rafaelmartins/fightstick/sch/fightstick.kicad_sch

## KiCad design sch/fightstick.kicad_sch (2026-01-09)

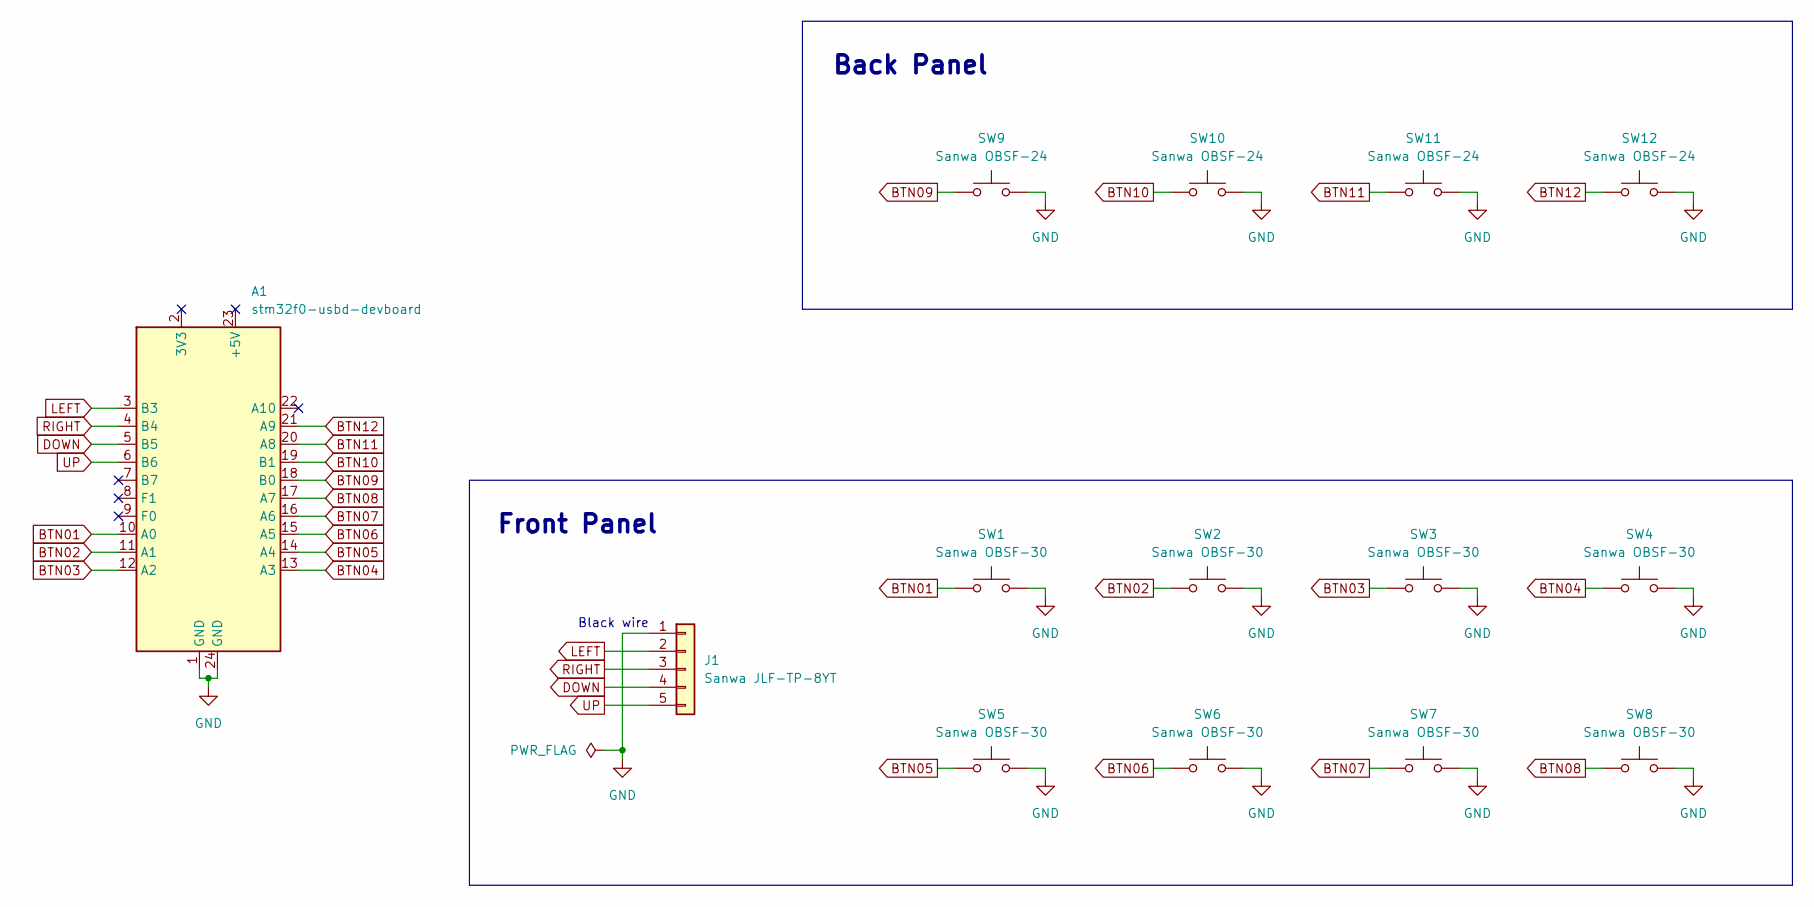
[picture p6: schematic fightstick.kicad_sch]

Parts:
A1: stm32f0-usbd-devboard
J1: Sanwa JLF-TP-8YT
SW1, SW2, SW3, SW4, SW5, SW6, SW7, SW8: Sanwa OBSF-30
SW9, SW10, SW11, SW12: Sanwa OBSF-24

Connections:
BTN01: A1.10 (A0), SW1.1
BTN02: A1.11 (A1), SW2.1
BTN03: A1.12 (A2), SW3.1
BTN04: A1.13 (A3), SW4.1
BTN05: A1.14 (A4), SW5.1
BTN06: A1.15 (A5), SW6.1
BTN07: A1.16 (A6), SW7.1
BTN08: A1.17 (A7), SW8.1
BTN09: A1.18 (B0), SW9.1
BTN10: A1.19 (B1), SW10.1
BTN11: A1.20 (A8), SW11.1
BTN12: A1.21 (A9), SW12.1
DOWN: A1.5 (B5), J1.4
GND: A1.1 (GND), A1.24 (GND), J1.1, SW1.2, SW2.2, SW3.2, SW4.2, SW5.2, SW6.2, SW7.2, SW8.2, SW9.2, SW10.2, SW11.2, SW12.2
LEFT: A1.3 (B3), J1.2
RIGHT: A1.4 (B4), J1.3
UP: A1.6 (B6), J1.5

Notes on the sheet:
Front Panel
Black wire
Back Panel
