rafaelmartins/fightstick/firmware/descriptors.c

// SPDX-FileCopyrightText: 2026 Rafael G. Martins <rafael@rafaelmartins.eng.br>
// SPDX-License-Identifier: BSD-3-Clause

#include <stdlib.h>

#include <usbd.h>
#include <usb-std-hid.h>

#define MANUFACTURER u"rgm.io"
#define PRODUCT      u"fightstick"

#define ID_VENDOR  0x1d50
#define ID_PRODUCT 0x619a

// +----------+-------+-------------------+
// | ReportId | Kind  | ReportSizeInBytes |
// +----------+-------+-------------------+
// |        1 | Input |                 2 |
// +----------+-------+-------------------+
static const uint8_t hid_report_descriptor[] =
{
    0x05, 0x01,    // UsagePage(Generic Desktop[0x0001])
    0x09, 0x05,    // UsageId(Gamepad[0x0005])
    0xA1, 0x01,    // Collection(Application)
    0x85, 0x01,    //     ReportId(1)
    0x09, 0x01,    //     UsageId(Pointer[0x0001])
    0xA1, 0x00,    //     Collection(Physical)
    0x09, 0x30,    //         UsageId(X[0x0030])
    0x09, 0x31,    //         UsageId(Y[0x0031])
    0x15, 0xFF,    //         LogicalMinimum(-1)
    0x25, 0x01,    //         LogicalMaximum(1)
    0x95, 0x02,    //         ReportCount(2)
    0x75, 0x02,    //         ReportSize(2)
    0x81, 0x02,    //         Input(Data, Variable, Absolute, NoWrap, Linear, PreferredState, NoNullPosition, BitField)
    0xC0,          //     EndCollection()
    0x05, 0x09,    //     UsagePage(Button[0x0009])
    0x19, 0x01,    //     UsageIdMin(Button 1[0x0001])
    0x29, 0x0C,    //     UsageIdMax(Button 12[0x000C])
    0x15, 0x00,    //     LogicalMinimum(0)
    0x95, 0x0C,    //     ReportCount(12)
    0x75, 0x01,    //     ReportSize(1)
    0x81, 0x02,    //     Input(Data, Variable, Absolute, NoWrap, Linear, PreferredState, NoNullPosition, BitField)
    0xC0,          // EndCollection()
};

static const usb_device_descriptor_t device_descriptor = {
    .bLength = sizeof(usb_device_descriptor_t),
    .bDescriptorType = USB_DESCR_TYPE_DEVICE,
    .bcdUSB = 0x0200,
    .bDeviceClass = 0,
    .bDeviceSubClass = 0,
    .bDeviceProtocol = 0,
    .bMaxPacketSize0 = USBD_EP0_SIZE,
    .idVendor = ID_VENDOR,
    .idProduct = ID_PRODUCT,
    .bcdDevice = 0x0101,
    .iManufacturer = 1,
    .iProduct = 2,
    .iSerialNumber = 3,
    .bNumConfigurations = 1,
};

const usb_device_descriptor_t*
usbd_get_device_descriptor_cb(void)
{
    return &device_descriptor;
}


typedef struct __attribute__((packed)) {
    usb_config_descriptor_t config_descriptor;
    usb_interface_descriptor_t interface_descriptor;
    usb_hid_descriptor_t hid_descriptor;
    usb_endpoint_descriptor_t endpoint_in_descriptor;
} config_descriptor_t;

static const config_descriptor_t config_descriptor = {
    .config_descriptor = {
        .bLength = sizeof(usb_config_descriptor_t),
        .bDescriptorType = USB_DESCR_TYPE_CONFIGURATION,
        .wTotalLength = sizeof(config_descriptor_t),
        .bNumInterfaces = 1,
        .bConfigurationValue = 1,
        .iConfiguration = 0,
        .bmAttributes = USB_DESCR_CONFIG_ATTR_RESERVED,
        .bMaxPower = 20, // 40mA
    },
    .interface_descriptor = {
        .bLength = sizeof(usb_interface_descriptor_t),
        .bDescriptorType = USB_DESCR_TYPE_INTERFACE,
        .bInterfaceNumber = 0,
        .bAlternateSetting = 0,
        .bNumEndpoints = 1,
        .bInterfaceClass = USB_DESCR_DEV_CLASS_HID,
        .bInterfaceSubClass = 0,
        .bInterfaceProtocol = 0,
        .iInterface = 0,
    },
    .hid_descriptor = {
        .bLength = sizeof(usb_hid_descriptor_t),
        .bDescriptorType = USB_DESCR_TYPE_HID,
        .bcdHID = 0x0111,
        .bCountryCode = 0,
        .bNumDescriptors = 1,
        .bDescriptorType2 = USB_DESCR_TYPE_HID_REPORT,
        .wDescriptorLength = sizeof(hid_report_descriptor),
    },
    .endpoint_in_descriptor = {
        .bLength = sizeof(usb_endpoint_descriptor_t),
        .bDescriptorType = USB_DESCR_TYPE_ENDPOINT,
        .bEndpointAddress = USB_DESCR_EPT_ADDR_DIR_IN | 1,
        .bmAttributes = USB_DESCR_EPT_ATTR_INTERRUPT,
        .wMaxPacketSize = USBD_EP1_IN_SIZE,
        .bInterval = 1,
    },
};

const usb_config_descriptor_t*
usbd_get_config_descriptor_cb(void)
{
    return &config_descriptor.config_descriptor;
}

const usb_interface_descriptor_t*
usbd_get_interface_descriptor_cb(uint16_t itf)
{
    switch (itf) {
    case 0:
        return &config_descriptor.interface_descriptor;
    }
    return NULL;
}


static const usb_string_descriptor_t language = {
    .bLength = 4,
    .bDescriptorType = USB_DESCR_TYPE_STRING,
    .wData = {0x0409},
};

static const usb_string_descriptor_t manufacturer = {
    .bLength = sizeof(MANUFACTURER),
    .bDescriptorType = USB_DESCR_TYPE_STRING,
    .wData = MANUFACTURER,
};

static const usb_string_descriptor_t product = {
    .bLength = sizeof(PRODUCT),
    .bDescriptorType = USB_DESCR_TYPE_STRING,
    .wData = PRODUCT,
};

const usb_string_descriptor_t*
usbd_get_string_descriptor_cb(uint16_t lang, uint8_t idx)
{
    (void) lang;
    switch (idx) {
    case 0:
        return &language;
    case 1:
        return &manufacturer;
    case 2:
        return &product;
    case 3:
        return usbd_serial_internal_string_descriptor();
    }
    return NULL;
}


bool
usbd_ctrl_request_get_descriptor_interface_cb(usb_ctrl_request_t *req)
{
    if (((uint8_t) req->wIndex != 0))
        return false;

    switch (req->bRequest) {
    case USB_REQ_GET_DESCRIPTOR:
        switch (req->wValue >> 8) {
        case USB_DESCR_TYPE_HID:
            usbd_control_in(&config_descriptor.hid_descriptor, config_descriptor.hid_descriptor.bLength, req->wLength);
            return true;

        case USB_DESCR_TYPE_HID_REPORT:
            usbd_control_in(&hid_report_descriptor, sizeof(hid_report_descriptor), req->wLength);
            return true;
        }
        break;
    }
    return false;
}
